pulikantitarun/astro-weather-india/stl_unified_v5/F5_Detent_Rod_PRINT_3.stl

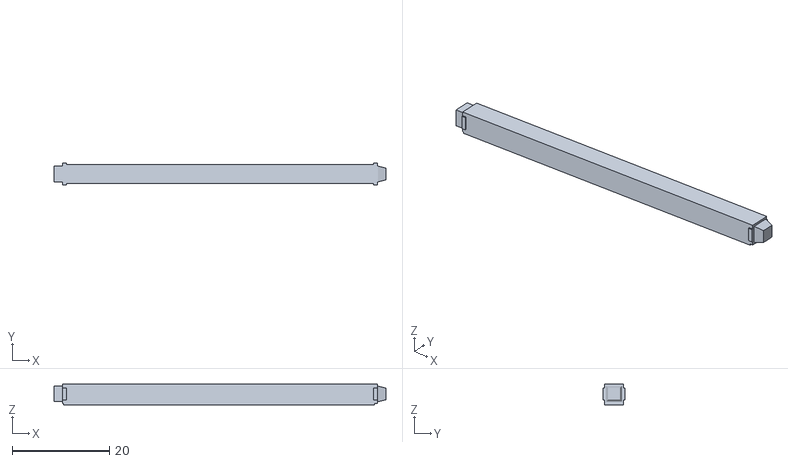
[picture p18: CAD file, 2026-07-29]
stl_unified_v5/F5_Detent_Rod_PRINT_3.stl
68.4 x 4.50 x 4.25
