pulikantitarun/astro-weather-india/firmware/AstroWeather_ESP32/secrets.example.h

#pragma once
#define WIFI_SSID "YOUR_WIFI_NAME"
#define WIFI_PASSWORD "YOUR_WIFI_PASSWORD"

// Used only until you change these from http://astroweather.local/settings.
// Settings username is always: admin
#define DEFAULT_ADMIN_PASSWORD "astroadmin"
#define DEFAULT_SETUP_AP_PASSWORD "astroclear"
